marqs85/snes_dejitter/rtl/snes_dejitter.v

// MIT License
// 
// Copyright (c) 2017-2018 Markus Hiienkari
// 
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

`define EDGE_SENSITIVE_CLKEN

module snes_dejitter(
    input MCLK_XTAL_i, //NTSC master clock source: 21.477272MHz from oscillator circuit
    input MCLK_EXT_i,  //PAL master clock source: 21.28137MHz (3-CHIP) or 17.73MHz (1-CHIP) from external source
    input MCLK_SEL_i,  //Output clock/csync mode: De-jitter/NTSC (0), Bypass/PAL (1)
    input CSYNC_i,
    output MCLK_XTAL_o,
    output GCLK_o,
    output CSYNC_o,
    output reg SC_o
);

wire mclk_ntsc = MCLK_XTAL_i;
wire mclk_ntsc_dejitter = mclk_ntsc & gclk_en;
wire mclk_pal = MCLK_EXT_i;

assign GCLK_o = MCLK_SEL_i ? mclk_pal : mclk_ntsc_dejitter;
assign CSYNC_o = MCLK_SEL_i ? CSYNC_i : csync_dejitter;

assign MCLK_XTAL_o = ~MCLK_XTAL_i;

reg [10:0] h_cnt;
reg [2:0] g_cyc;
reg csync_prev;
reg csync_dejitter;
reg gclk_en;
reg [1:0] sc_ctr;


always @(posedge mclk_ntsc) begin
    if ((h_cnt >= 1024) && (csync_prev==1'b1) && (CSYNC_i==1'b0)) begin
        h_cnt <= 0;
        if (h_cnt == 340*4-1)
            g_cyc <= 4;
        else
            csync_dejitter <= CSYNC_i;
    end else begin
        h_cnt <= h_cnt + 1'b1;
        if (g_cyc > 0)
            g_cyc <= g_cyc - 1'b1;
        if (g_cyc <= 1)
            csync_dejitter <= CSYNC_i;
    end

    csync_prev <= CSYNC_i;
end

always @(posedge mclk_ntsc) begin
    if (sc_ctr == 2'h2) begin
        sc_ctr <= 2'h0;
        SC_o <= ~SC_o;
    end else begin
        sc_ctr <= sc_ctr + 2'h1;
    end
end

`ifdef EDGE_SENSITIVE_CLKEN
//Update clock gate enable signal on negative edge
always @(negedge mclk_ntsc) begin
    gclk_en <= (g_cyc == 0);
end
`else
//ATF1502AS macrocells support D latch mode,
//enabling level sensitive update of gclk_en during negative phase
always @(*) begin
    if (!mclk_ntsc)
        gclk_en <= (g_cyc == 0);
end
`endif

endmodule
